o0morgan0o/BeAPad_Leds/src/FadeInFadeOutLightStrategy.cpp

//
// Created by morgan on 4/27/2022.
//

#include "FadeInFadeOutLightStrategy.h"
#include "LedBoard.h"

void FadeInFadeOutLightStrategy::reset() {
    _birthTime = _context->getCurrentTime();
    _currentLife = 0;
    fraction = 0;

}

void FadeInFadeOutLightStrategy::updateValues(unsigned long currentTime) {
    fraction += 1;
    CRGB newColor = blend(_channelBaseColor, CRGB::Red, fraction);
    _lifeSpan = _context->getCurrentTime() - _birthTime;
    for (uint8_t i = 0; i < _context->NUM_PIXELS; i++) {
        _ledColorsInStrategy[i] = newColor;
    }
}

void FadeInFadeOutLightStrategy::reinit(unsigned long currentTime) {
    fraction = 0;
    _birthTime = _context->getCurrentTime();

}

void FadeInFadeOutLightStrategy::triggerOn() {
    fraction = 0;
    for (uint8_t i = 0; i < _context->NUM_PIXELS; i++) {
        _ledColorsInStrategy[i] = _channelBaseColor;
    }
}

void FadeInFadeOutLightStrategy::triggerOff() {

}
