o0morgan0o/BeAPad_Leds/src/FadeOutLightStrategy.cpp

//
// Created by morgan on 4/26/2022.
//

#include "FadeOutLightStrategy.h"
#include "LedBoard.h"
#include "LedBoardsManager.h"

FadeOutLightStrategy::FadeOutLightStrategy(LedBoard *context) : LightStrategy(context) {}

void FadeOutLightStrategy::reset() {
    _birthTime = _context->getCurrentTime();
}

void FadeOutLightStrategy::updateValues(unsigned long currentTime) {
    for (uint8_t i = 0; i < _context->NUM_PIXELS; i++) {
        _ledColorsInStrategy[i].fadeToBlackBy(10);
    }
    _lifeSpan = _context->getCurrentTime() - _birthTime;
}

void FadeOutLightStrategy::reinit(unsigned long currentTime) {
    _birthTime = _context->getCurrentTime();
}

void FadeOutLightStrategy::triggerOn() {
    for (uint8_t i = 0; i < _context->NUM_PIXELS; i++) {
        _ledColorsInStrategy[i] = _channelBaseColor;
    }
}

void FadeOutLightStrategy::triggerOff() {

}
