o0morgan0o/BeAPad_Leds/src/LightStrategy.h

//
// Created by morgan on 4/25/2022.
//

#ifndef PLATFORMIO_PROGRAM_LIGHTSTRATEGY_H
#define PLATFORMIO_PROGRAM_LIGHTSTRATEGY_H

#include "RGB_Color.h"

#ifdef IN_TESTING
#include "../test/Fake_CRGB.h"
#else

#include <FastLED.h>

#endif
#define MAX_NUMBER_OF_LEDS_PER_BOARD 20

class LedBoard;

enum class LIGHT_STRATEGIES {
    NO_LIGHT_STRATEGY,
    STRATEGY_FULL_LIGHT,
    STRATEGY_FADE_OUT,
    STRATEGY_FADE_IN_AND_FADE_OUT,
    STRATEGY_SERPENTIN,
    STRATEGY_FLASH_TOWARDS_EXTERIOR,
    STRATEGY_SHIFT_KEY_STRATEGY

};

class LightStrategy {
public:
    explicit LightStrategy(LedBoard *context);

    virtual ~LightStrategy() = default;

    virtual void reset() = 0;

    virtual void updateValues(unsigned long currentTime) = 0;

    virtual void triggerOn() = 0;

    virtual void triggerOff() = 0;

    virtual void reinit(unsigned long currentTime) = 0;

    virtual unsigned long getLifeSpan() { return _lifeSpan; }

    virtual unsigned long getBirthTime() { return _birthTime; }

    virtual void setBaseColor(CRGB color);

    virtual CRGB getBaseColor();

    virtual CRGB getSpecificLedColor(uint8_t index);

protected:
    unsigned long _lifeSpan{};
    unsigned long _currentLife{};
    unsigned long _birthTime{};
    CRGB _channelBaseColor{0, 0, 0};
    LedBoard *_context{};
    CRGB _ledColorsInStrategy[MAX_NUMBER_OF_LEDS_PER_BOARD]{CRGB::Black};

};

#endif //PLATFORMIO_PROGRAM_LIGHTSTRATEGY_H
