o0morgan0o/BeAPad_Leds/src/NoLightStrategy.cpp

//
// Created by morgan on 4/25/2022.
//

#include "NoLightStrategy.h"
#include "LedBoard.h"

void NoLightStrategy::reset() {
    _channelBaseColor = CRGB::Black;
}

void NoLightStrategy::updateValues(unsigned long currentTime) {

}

void NoLightStrategy::triggerOn() {
    for(uint8_t i = 0; i <  _context->NUM_PIXELS; i++){
        _ledColorsInStrategy[i] = CRGB::Black;
    }

}

void NoLightStrategy::triggerOff() {


}

void NoLightStrategy::reinit(unsigned long currentTime) {
    _channelBaseColor = CRGB::Black;
    for (uint8_t i = 0; i < _context->NUM_PIXELS; i++) {
        _ledColorsInStrategy[i] = CRGB::Black;
    }

}
