o0morgan0o/BeAPad_Leds/src/SerpentinSingleLed.h

//
// Created by morgan on 5/15/2022.
//

#ifndef PLATFORMIO_PROGRAM_SERPENTINSINGLELED_H
#define PLATFORMIO_PROGRAM_SERPENTINSINGLELED_H
#ifdef IN_TESTING
#include "../test/Fake_CRGB.h"
#else

#include <FastLED.h>

#endif

class SerpentinSingleLed {
public:
    explicit SerpentinSingleLed() = default;

    void setDelayBeforeStartAndLifeExpectancy(unsigned long delayBeforeStart, unsigned long lifeExpectancy) {
        _delayBeforeStart = delayBeforeStart;
        _initialLifeExpectancy = lifeExpectancy;
    }

    void reborn(unsigned long time) {
        _birthTime = time;
        _startTime = _birthTime + _delayBeforeStart;
        _lifeExpectancy = _initialLifeExpectancy;
        _endTime = _startTime + _lifeExpectancy;
    }

    CRGB getColorAtTime(unsigned long currentTime) const {
        if (getIsInLifeSpan(currentTime))
            return _colorWhenOn;
        else {
            return _colorWhenOff;
        }
    }

    bool getIsInLifeSpan(unsigned long currentTime) const {
        if (currentTime >= _startTime && currentTime < _endTime) {
            return true;
        } else {
            return false;
        }

    }

    void forceDeath(unsigned long currentTime) {
        _endTime = currentTime;
//        _lifeExpectancy = 0;
    }

    void setColors(CRGB colorWhenOn, CRGB colorWhenOff) {
        _colorWhenOn = colorWhenOn;
        _colorWhenOff = colorWhenOff;
    }

    double getDelayBeforeStart() const {
        return _delayBeforeStart;
    }

    double getLifeExpectancy() const {
        return _lifeExpectancy;
    }

    double getStartTime() const {
        return _startTime;
    }

public:
    CRGB _colorWhenOn{CRGB::White};
    CRGB _colorWhenOff{CRGB::Black};
private:
    unsigned long _endTime{0};
    unsigned long _delayBeforeStart{0};
    unsigned long _initialLifeExpectancy{0};
    unsigned long _lifeExpectancy{0};
    unsigned long _birthTime{0};
    unsigned long _startTime{0};

};

#endif //PLATFORMIO_PROGRAM_SERPENTINSINGLELED_H
