o0morgan0o/BeAPad_Leds/src/FadeInFadeOutLightStrategy.h

//
// Created by morgan on 4/27/2022.
//

#ifndef PLATFORMIO_PROGRAM_FADEINFADEOUTLIGHTSTRATEGY_H
#define PLATFORMIO_PROGRAM_FADEINFADEOUTLIGHTSTRATEGY_H


#include "LightStrategy.h"

class FadeInFadeOutLightStrategy : public LightStrategy {
public:
    explicit FadeInFadeOutLightStrategy(LedBoard *context) : LightStrategy(context) {}

    void reset() override;

    void updateValues(unsigned long currentTime) override;

    void triggerOn() override;

    void triggerOff() override;

    void reinit(unsigned long currentTime) override;

    uint8_t fraction = 0;

};

#endif //PLATFORMIO_PROGRAM_FADEINFADEOUTLIGHTSTRATEGY_H
