o0morgan0o/BeAPad_Leds/src/RGB_Color.h

//
// Created by morgan on 4/25/2022.
//

#ifndef PLATFORMIO_PROGRAM_RGB_COLOR_H
#define PLATFORMIO_PROGRAM_RGB_COLOR_H

#include <cstring>

struct RGB_Color {
    RGB_Color(uint8_t _r, uint8_t _g, uint8_t _b) {
        r = _r;
        g = _g;
        b = _b;
    }

    uint8_t r;
    uint8_t g;
    uint8_t b;


};

#endif //PLATFORMIO_PROGRAM_RGB_COLOR_H
